Grotesmurf696/ZUIN/reports and protocols/Develop III/Rapport  CMF 02.pdf

# Protocol CMF usertests

# Project informatie

Projectnaam: Zuin
Zuin is een slim product voor kinderen dat hen bewust maakt van verbruik in huis en hen stimuleert om de interactie aan te gaan met hun ouders om energiezuiniger te leven.

Interviewer:
- Sam Verkimpe (Sam.Verkimpe@UGent.be), Student Industrieel Ingenieur Industrieel Ontwerpen
- Maxim Depever (Maxim.Depever@UGent.be), Student Industrieel Ingenieur Industrieel Ontwerpen
- Jitse Van Laer (Jitse.VanLaer@Ugent.be), Student Industrieel Ingenieur Industrieel Ontwerpen

# Algemeen

Het ZUÏN horloge bestaat uit een aantal kenmerkende onderdelen, zo heb je het bandje en de body die uit verschillende materialen gemaakt kan worden, de tactile ring die een verischillend patroon en tactile feel kan hebben als ook de finish van de body en het scherm.
Tijdens deze usertest gaat een groep kinderen opgedeeld worden in kleinere groepen. Ze krijgen de mogelijkheid om gedurende een bepaalde periode naar alle prototypes te kijken en ze uit te testen. Waarna ze een vragenblad kunnen invullen over de prototypes die ze net getest hebben. Erna volgt nog een kort vragenrondje om wat randinformatie te weten te komen over kleuren.

# Recrutering

Doordat Sam een aantal jaar leiding heeft gegeven in de scouts was er de mogelijkheid om via de huidige leiding een mail te laten rondsturen naar de ouders van de leden die in de “Woudloper” tak zitten. De leden binnen deze tak zijn hier max. 12 jaar oud, dus dit is de perfecte tak om testen uit te voeren. Aangezien de leden elke zondag activiteit hebben op de scouts zou het makkelijk zijn om met een selecte groep kinderen een half uurtje vroeger af te spreken om zo net voor de activiteit de usertest af te nemen.
Hieronder (zie Figure 1)staat een kopie van de mail die via één van de huidige leiding van de woudlopers naar alle ouders gestuurd is. In de bijlage van deze mail stond dan ook de informed consent die de ouders konden ondertekenen.

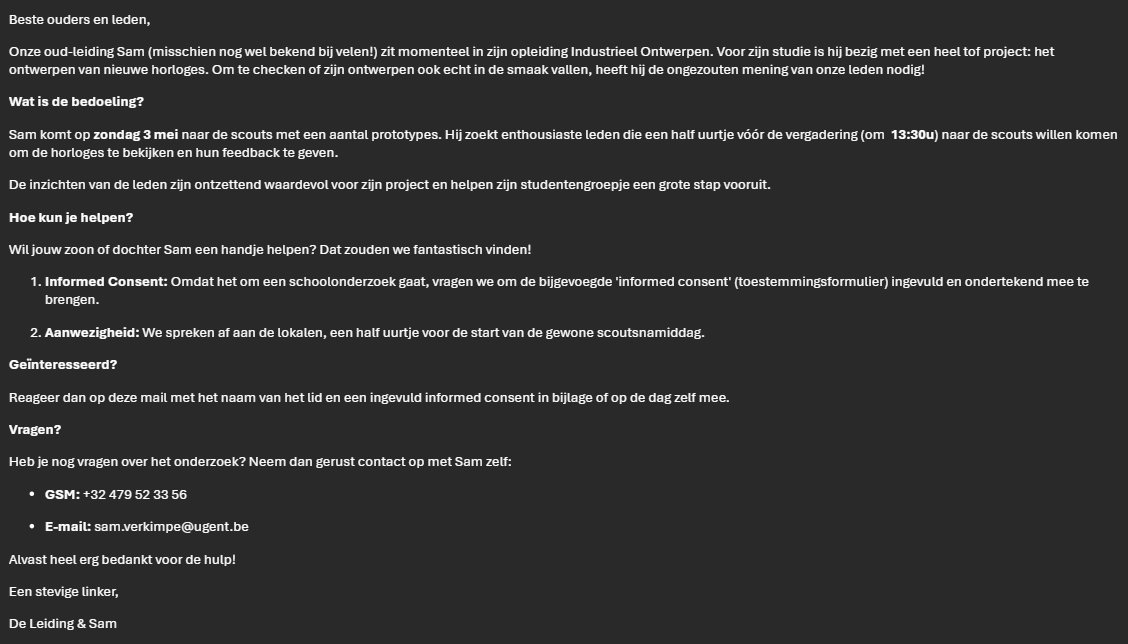
[picture p4: figure]

Figure 1: Rectuteringsmail
Door beperkte reactie op de mail was er besloten om de test met één week te verlaten naar zondag 10 mei, op 2 mei werd er na afloop van de activiteit een flyer uitgedeeld die de kinderen mee naar huis konden nemen. Zo wisten de kinderen van de activiteit en zouden zij zo rechtstreeks de ouders aan kunnen spreken voor op deze manier hopelijk toch een stuk meer respondenten te krijgen. Op onderstaande afbeelding (zie Figuur 1: Flyer voor leden) is de flyer te zien die de kinderen mee naar huis kregen.

# Respondenten (N = 3)

Kind | Leerjaar | Datum | Plaats
Enzo | 5 | 30/04/2026 | Scouts Wondelgem
Riven | 5 | 30/04/2026 | Scouts Wondelgem
Myron | 5 | 30/04/2026 | Scouts Wondelgem

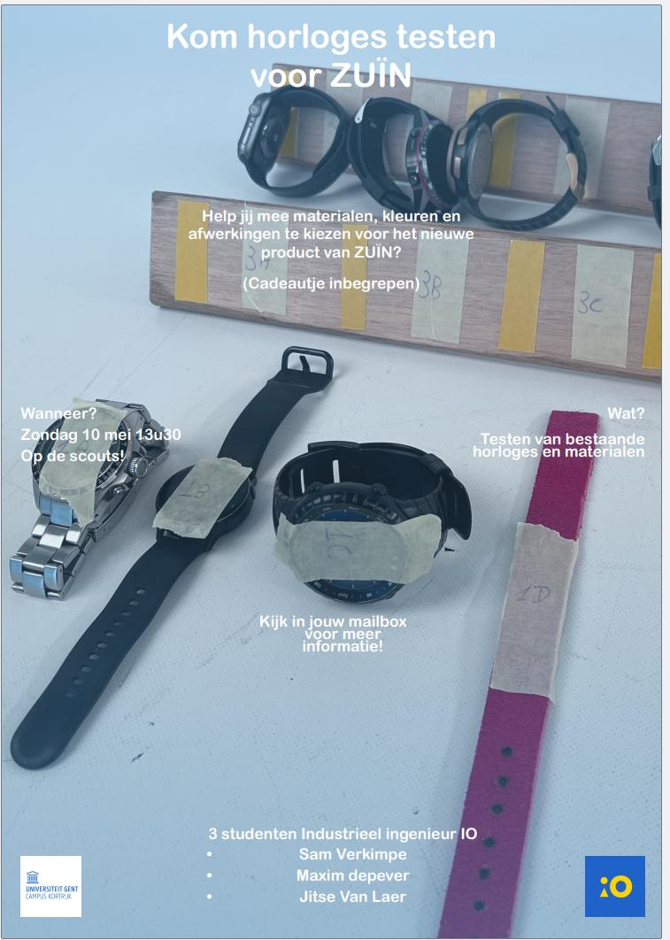
[picture p5: figure]

Figuur 1: Flyer voor leden

# Prototypes

Voor de testartefacten worden zowel zelfgemaakte prototypes als ook horloges van andere merken gebruikt. Dit zorgt ervoor dat er op een makkelijke manier een heel breed scala aan materialen en finishes getest kunnen worden. Voor het patroon op de ring worden er 4 body’s van horloge’s geprint. Elk van de 4 heeft een ander profiel op de ring, maar ook een andere taclite feedback. Voor het materiaal van de bandjes en de finishes van de body’s worden er horloges van andere merken gebruikt. De kinderen worden dan gevraagd om enkel naar één van de aspecten te kijken. Op onderstaande afbeelding (zie Figure 2) is de volledige testopstelling te zien van alle artefacten.

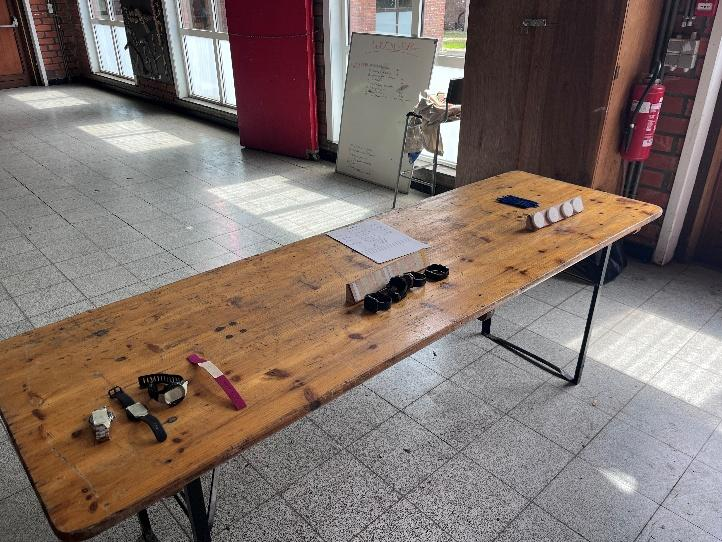
[picture p6: figure]

Figure 2: Testopstelling
Er zijn in totaal 3 “boards” met artefacten die de kinderen kunnen aandoen of waar ze aan kunnen voelen. Op deze manier is het makkelijker om de test op te delen in 3 groepen zodat elke groep telkens een ander deel van de gehele CMF ervaring test.

## Board 1

Bij deze setup is het de bedoeling dat de kinderen de artefacten (3 horloges en 1 prototype horloge bandje) rond hun pols doen en ze even goed voelen zodat ze god de verschillen tussen de bandjes merken. Op onderstaande afbeelding (zie Figure 3) zijn de 4 artefacten te zien, waaronder testartefact 1D. Dit bandje is gemaakt van een synthetisch leer. Het kleur van het bandje zelf speelt hier geen grote rol, maar vooral het gevoel rond de pols.

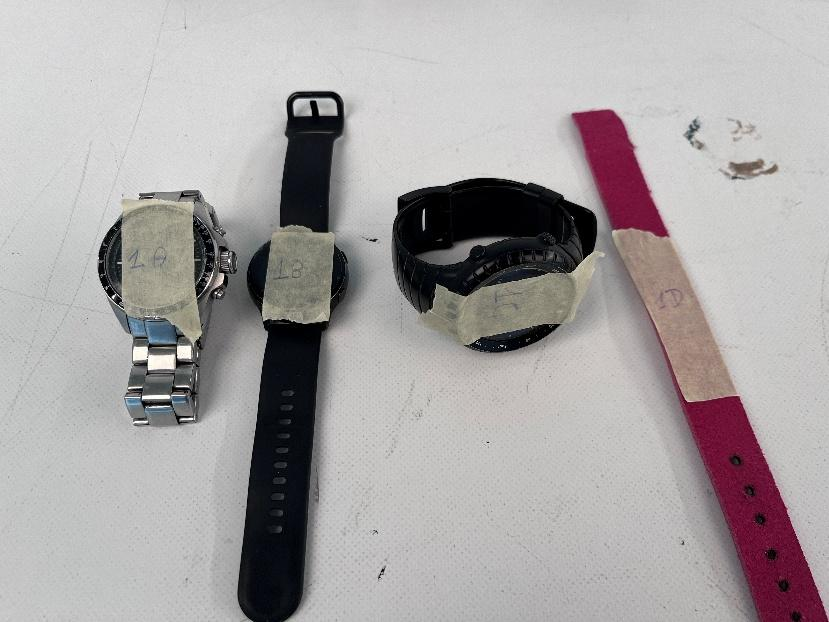
[picture p7: figure]

Figure 3: Board 1

## Board 2

Op Board 2 zijn 4 horloges te zien, dit zijn zowel smartwatches als normale digitale horloges. Hier moeten de kinderen kijken naar het materiaal en de finishes waarvan de body’s gemaakt zijn. Ook de afwerking op de knoppen speelt hier een rol. De kinderen mogen voelen aan de horloges, maar de horloges aandoen wordt hier niet gedaan. Op onderstaande afbeelding (zie Figure 4) is het 2de board te zien.

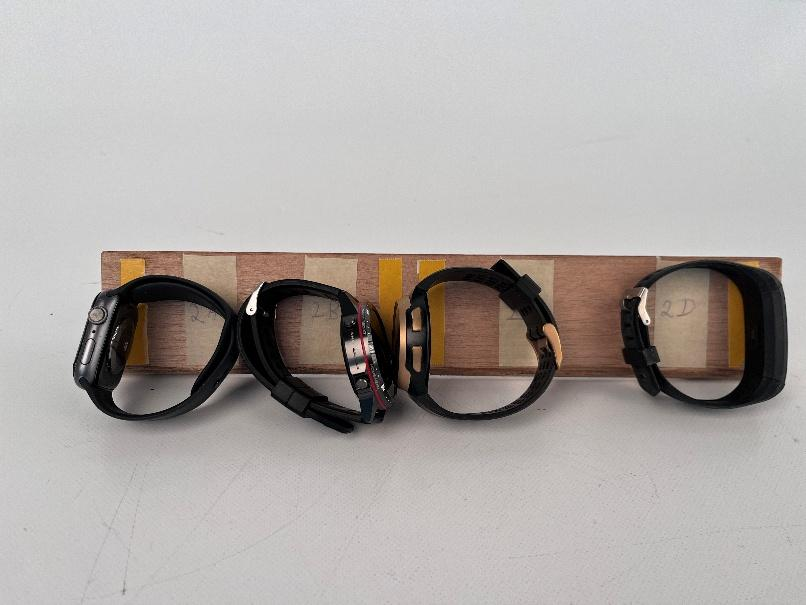
[picture p8: figure]

Figure 4: Board 3

## Board 3

Op board 3 worden de 4 verschillende prototypes van body’s geplaatst. De kinderen kunnen hier draaien aan de ringen van de body’s en op deze manier voelen hoe de afwerking op de ring is, als ook hoe de tactile feedback van de draaibeweging zelf is.

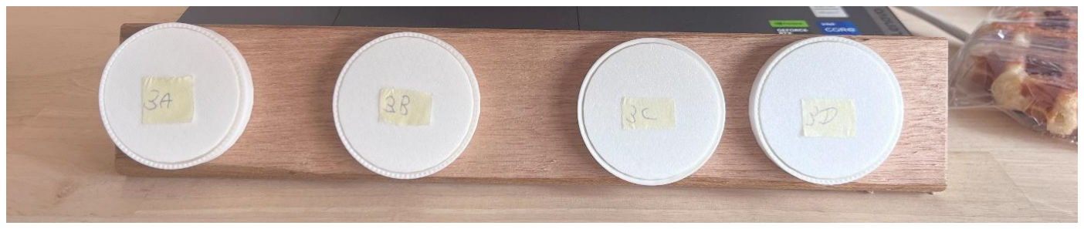
[picture p9: figure]

# Vragenlijst

Tijdens het testen worden de kinderen gevraagd om een vragenlijst in te vullen. Via deze vragenlijst willen we beter te weten komen wat de kinderen van de verschillende prototypes. Ze worden gevraagd om via een likertscale aan te duiden wat en hoe ze de verschillende prototypes ervaren. In bijalge zijn alle vragenlijsten te zien.

# Rapport

Het rapport van deze usertest is hier te vinden: CMF_Rapport_Develop2.pdf (https://ugentbe-my.sharepoint.com/:b:/g/personal/sam_verkimpe_ugent_be/IQCc59gRmQsRSLWiW1mBbghMAdhwbeE4el2uZ555LbgcBAo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)

# Vragenlijst

De vargenlijst voor de leden is hier te vinden: Vragenlijst voor leden.pdf (https://ugentbe-my.sharepoint.com/:b:/g/personal/sam_verkimpe_ugent_be/IQAT-k2qmfA6Qpb_IdjVv9tHARlVMj0OQpazggyW6qtySMU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)
