Grotesmurf696/ZUIN/img/Flyer voor leden_V2.pdf

# Kom horloges testen voor ZUÏN

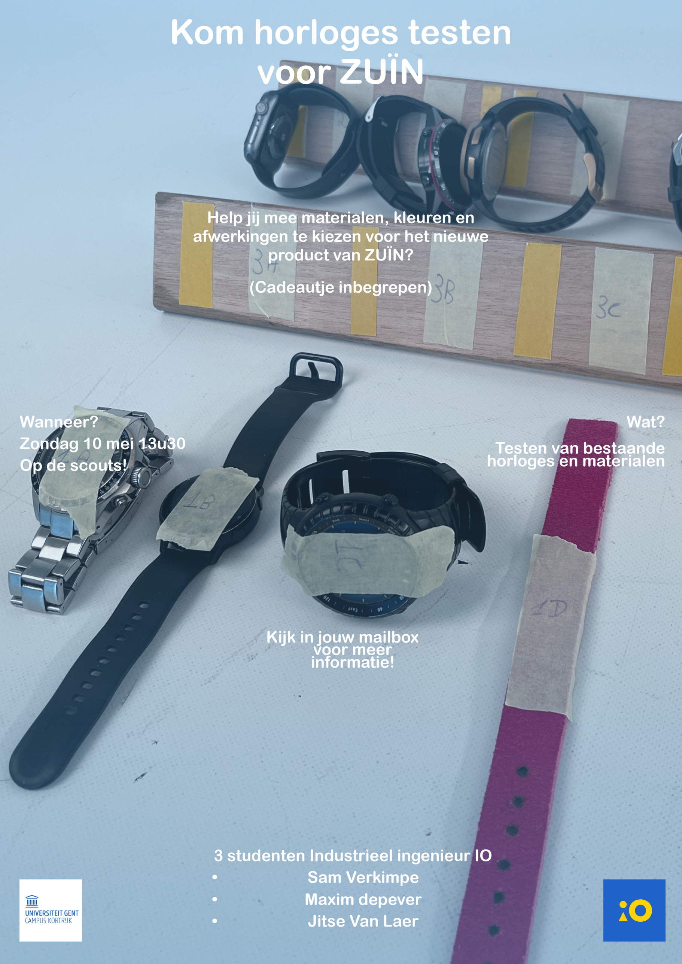
[picture p10: page 1]

Wanneer?
Zondag 10 mei 13u30
Op de scouts!

Wat?

Testen van bestaande
horloges en materialen

Help jij mee materialen, kleuren en afwerkingen te kiezen voor het nieuwe product van ZUÏN?

(Cadeautje inbegrepen)

### 3 studenten Industrieel ingenieur IO

- Sam Verkimpe
- Maxim depever
- Jitse Van Laer

Kijk in jouw mailbox
voor meer
informatie!
