Grotesmurf696/ZUIN/reports and protocols/Develop I/Rapport interview develop I.pdf

# Interview report – develop 1 (N=5)

## Project informatie

Projectnaam: Zuin
Zuin is een slim product voor kinderen dat hen bewust maakt van verbruik in huis en hen stimuleert om de interactie aan te gaan met hun ouders om energiezuiniger te leven.

Interviewer:
- Sam Verkimpe (Sam.Verkimpe@UGent.be), Student Industrieel Ingenieur Industrieel Ontwerpen
- Maxim Depever (Maxim.Depever@UGent.be), Student Industrieel Ingenieur Industrieel Ontwerpen
- Jitse Van Laer (Jitse.VanLaer@Ugent.be), Student Industrieel Ingenieur Industrieel Ontwerpen

## Doelstelling en kadering

In het 1ste deel van de develop-fase wordt ingezet om van concept naar een onderbouwde functionele architectuur te gaan. Er wordt dieper gezocht naar de koopbereidheid van het product. Verder wordt er ook ingegaan op de gewenste functionaliteiten waarvan enerzijds de ouders denken dat hun kind het leuk gaat vinden en anderzijds de functies die de ouders overtuigen om het product te kopen voor hun kind.

## Methode + reden

In het eerste deel van de Develop-fase is bewust gekozen om gebruikersinterviews af te nemen, maar deze keer gericht op de ouders. Dit zijn namelijk de personen die effectief de stap moeten zetten om het product te kopen. In de interviews werd de koopbaarheid afgetoetst. Verder werd er aan de hand van card sorting gekeken welke functies de ouders interessant vinden en een meerwaarde vinden aan het product. Uiteindelijk werd er nog gevraagd achter de ervaringen met habit changing products en de invloed hiervan. Er werd gekozen om interviews af te nemen om zo in gesprek te kunnen gaan met de ouder en door te vragen op bepaalde interessante antwoorden en keuzes.

## Protocol

Interview - protocol.docx (https://ugentbe-my.sharepoint.com/:w:/g/personal/sam_verkimpe_ugent_be/IQB2XM7peNSuRbQRF3uczHEGATVunaRYGWqFntXtGxvA77w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)

## Respondenten

- Steekproefomschrijving (N = 5)
De respondenten zijn ouders die kinderen hebben in de lagere school. Ze werden gecontacteerd via de lagere school van hun kind om vrijwillig deel te nemen aan dit interview.

## Interview

Interview 1: Sara

1. Huidige houding tegenover duurzaamheid & verbruik
- Niet actief aanwezig in gezingsleven
- Tijd en mentale ruimte ontbreken om hier actief mee bezig te zijn
- Wel de standaarddingen, zoals lichten uitdoen & verwarming regelen
- Facturen worden niet geanalyseerd
- Ze vindt het wel belangrijk voor de toekomst van haar kinderen, vooral gezien de stijgende energieprijzen
- Kinderen worden thuis toch weinig betrokken
- Op school wordt wel al een basis aangeleerd
2. Koopbaarheid
- Niet spontaan kopen -> ze is zelf niet actief of bewust bezig met energieverbruik & duurzaamheid
- In een bundel (bv via energieleverancier) is drempelverlagend
- Extra optie bij dienst maakt bewuster
- Extra info zou helpen
Ouder | Leeftijd Kind | Zonnepanelen? | Datum | Plaats
Sara | 12 & 8 | Nee | 28/2/2026 9u | Thuis
Marie | 8 | Ja | 28/2/2026 10u | Thuis
Lena | 5 & 8 | Ja | 28/2/2026 11u | Thuis
Bram | 5 & 6 | Nee | 2/3/2026 10u | Online
Jonas | 4 & 7 | Ja | 5/3/2026 20u | Online

3. Functies
- Minder aantrekkelijk
- Sterke prikkels
- Fysieke knoppen ->
touchscreen voelt actueler
- Aantrekkelijk
- Virtueel huisdier -> speels & motiverend
- Challenges
- Gezinscompetitie
- Subtiel geluidje bij over verbruik

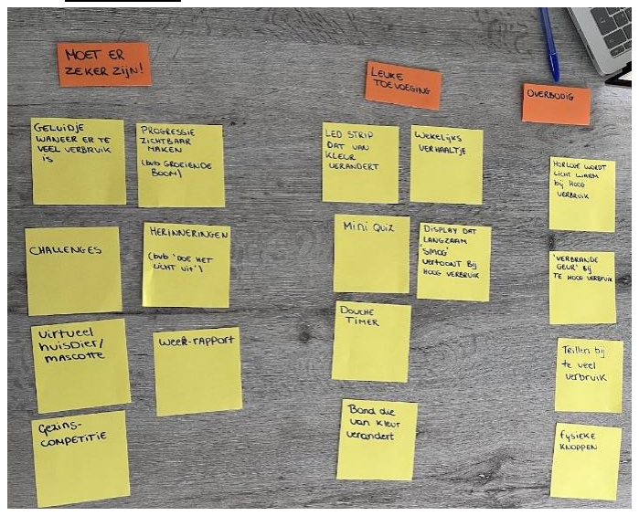
[picture p59: figure]

4. Ervaringen met smart devices & habit changing products
- Probeerde recent kleine “geluksmomenten” op te schrijven, maar hield dat slechts enkele dagen vol
- Ze is een overdenker
- Tijdsgebrek

Interview 2: Marie

1. Huidige houding tegenover duurzaamheid & verbruik
- “Waarschijnlijk te weinig”
- Wel de basisdingen
- Lichten uitdoen
- Verwarming instellen
- Huis geïsoleerd
- Zonnepanelen
- Partner houdt zich wel actief bezig met facturen en verbruik
- Ze kiest bewust voor praktisch gemak & rust in haar hoofd -> bijvoorbeeld niet altijd rekening kunnen houden met zonne-uren
- Dochter leert op school over duurzaamheid
- Ze zou haar houders aanspreken op lichten laten branden
2. Koopbereidheid
- Afhankelijk van de prijs
- Eerder zelf kopen dan via een energieleverancier
- Kan er dan makkelijker meer info over zoeken
- “Dan denk ik: Amai, wat willen ze ons weer smeren?”
- Via leverancier voelt gepusht

3. Functies
- Minder aantrekkelijk
- Trillen (enkel als het verbruik echt extreem is -> afhankelijk
van hoe vaak)
- Te veel visuele prikkels
- Overmatige ‘nieuwe’ functies
- Complexe of flashy features
- “Ik ben zo wel doe-maar-gewoon-normaal”
- Aantrekkelijk
- Virtueel huisdier
- Zichtbare progressie
- Belonen

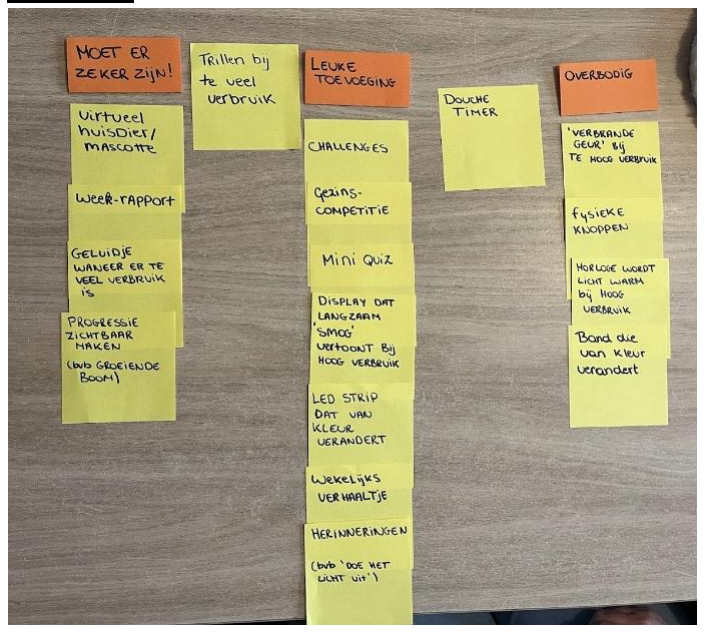
[picture p60: figure]

4. Ervaringen met smart devices & habit changing products
- De kinderen hadden vroeger speelgoed zoals een virtueel diertje (Bitsy)
- Intens gebruik in begint -> daarna in speelgoedbak
- “Ik denk dat dat met zo'n horloge ook zou kunnen, dat dat na een maand of zo gedaan is geweest. Maar als je dat aandoet, dan kun je dat al niet kwijt geraken.”
- Geen slimme energiemeters, app van zonnepanelen wordt niet opgevolgd, geen actieve monitoring van verbruik
- Dochter heeft een slaapdagboek
- Houdt dit enkel vol als de mama het begeleidt

Interview 3: Lena

1. Huidige houding tegenover duurzaamheid & verbruik
- Maakt zelf wasmiddel
- Probeert vaker de fiets te nemen
- Zonnepanelen
- Probeert wasmachine & vaatwasser te plannen op zonnige momenten
- Spreekt haar kinderen actief aan op lichten uitdoen
- Kinderen doen goed meer
2. Koopbereidheid
- Ze zou het misschien kopen als de kinderen ouder zijn
- Als app zou het meer aanspreken
- Kinderen gaan ook spelletjes willen spelen op het horloge niet enkel de tijd zien

3. Functies

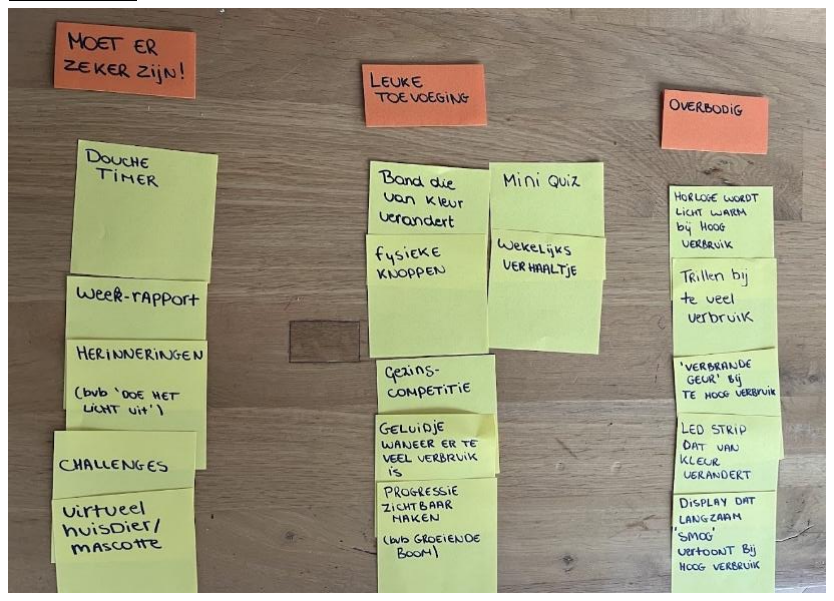
[picture p61: figure]

- Minder aantrekkelijk
- Trillen bij hoog verbruik -> went mogelijk snel
- “Ik denk dat dat na een tijd ook niet meer opvalt als dat afgaat.”
- Afleiding mag niet overheersen
- Aantrekkelijk
- Virtueel huisdier
- Challenges
- Douche timer -> herkenbaar probleem
- Rapport / overzicht
- Herinneringen
4. Ervaringen met smart devices & habit changing products
- Zoon heeft een bitsy = tamagotchi-achtig diertje waarvoor je moet zorgen
- Virtuele diertjes zijn gekend en positief ervaren (zoomorphisme)
- Zelf enkel een app voor zonnepanelen en elektriciteit app
- Geen actieve monitoring
- Nog nooit een dagboek of langdurige tracking geprobeerd
- “Ik ben misschien te chaotisch daarvoor”
- “Als ik met iets nieuws begin, houd ik het niet lang vol”

Interview 4: Bram

1. Huidige houding tegenover duurzaamheid & verbruik
- Focust op verspilling te beperken & kinderen worden erop aangesproken
- Lichten uitdoen
- Kraan dichtdraaien
- Geen eten/drinken laten staan => bewust aankopen doen
- Niet dagelijks vlees eten

- Duurzaamheid zit in gewoontes, niet in grote spectaculaire acties
2. Koopbereidheid
- Leeftijd is een cruciale factor
- 5-6 jaar is te jong voor hem omdat kinderen op die leeftijd pas klok leren lezen
- Eerder geschikt voor wanneer kinderen het concept van geld begrijpen, wanneer ze oorzaak-gevolg kunnen koppelen en wanneer competitie hen echt motiveert
- Doelgroep rond 8-12 jaar
- “Ik vind dat een kind op zoveel mogelijk fronten moet proberen een
- kind te blijven, zonder te veel input of dingen waar ze eigenlijk in principe nog niet zoveel aan kunnen doen.”
- Product moet een competitief element bevatten en er moet een concreet doel aan gekoppeld zijn
3. Functies

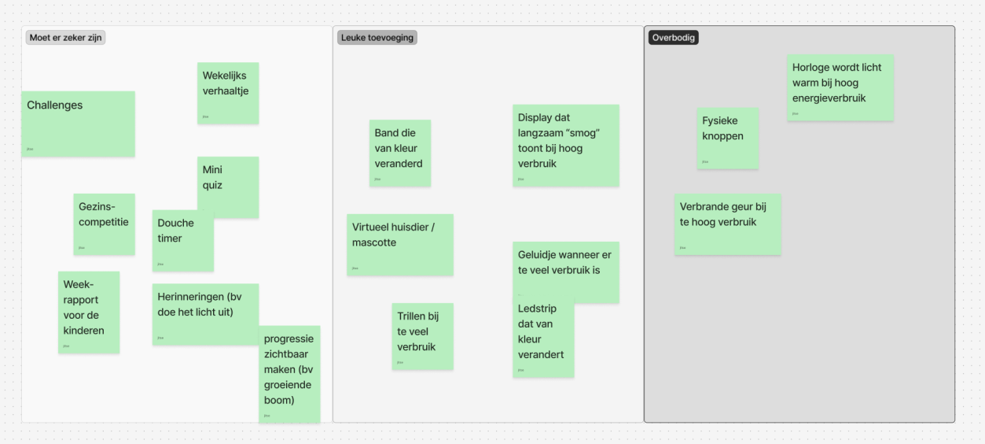
[picture p62: figure]

- Minder aantrekkelijk
- Trillen
- Constant signalen
- Warm worden
- Overmatige fysieke prikkels
- Aantrekkelijk
- Rapport
- Zichtbare progressie
- Quiz of verhaaltje met educatieve waarde
- Meetbaar resultaat
- Competitie
- Concreet doel
- “Wat ik het belangrijkste vind is dat er wel effectief een resultaat wordt gekoppeld aan het doel, maar het resultaat moet ook iets bijleren, natuurlijk.”

4. Ervaringen met smart devices & habit changing products
- Willen in de toekomst verwarming, zonnepanelen en hun energiebeheer in 1 systeem koppelen (hebben net een nieuw huis)
- Habit changing products: trainingsschema & budgetbeheer
- Tools werken alleen als ze zichtbaar aanwezig zijn
- “Als ik iets moet opendoen om dat dan te doen, dat gaat niet. Als ik dat zie of dat is bijvoorbeeld een smartbord of iets van dienen aard, dan gaat dat vanzelf.”

Interview 5: Jonas

1. Huidige houding tegenover duurzaamheid & verbruik
- Bezig maar op gezond verstand
- Zonnepanelen -> wasprogramma’s daarop afstemmen
- Elektrische auto’s
- Geen onbewust stroomverbruik
- Hoort bij orde & netheid in opvoeding
- In onderbewustzijn
- Elektriciteit nog moeilijk want is iets onuitputtelijk voor hen
- Toestellen op batterijen zijn wel meer begrijpbaar
2. Koopbereidheid
- De gamification (de badges & notifications) werkt bij kinderen
- Als ouder niet direct kopen want kinderen moeten het concept van energie nog leren, om handelingen te koppelen aan verbruik (bv dat koken een piekmoment zal zijn) moeten ze ouder voor zijn
- Alles van wearables als ouder wel nadenken wat er met gegevens wordt gedaan -> als je dit gratis krijgt bij energieleverancier gaan zij misschien deze datapunten kunnen gebruiken -> extra over nadenken
3. Functies

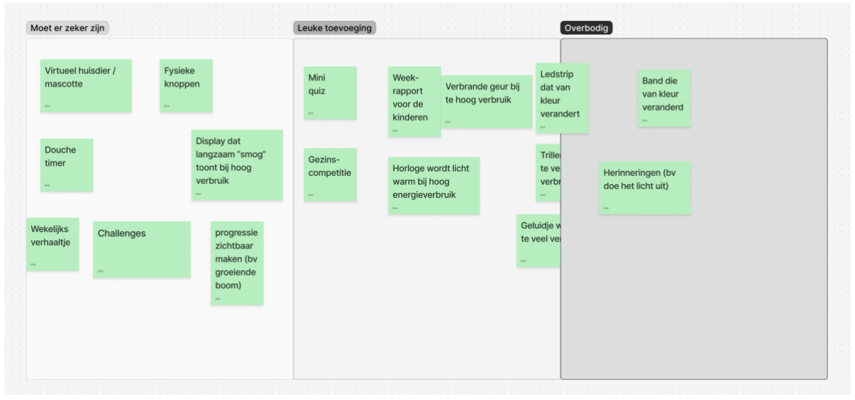
[picture p63: figure]

- Minder aantrekkelijk
- “Mensen krijgen al zoveel notificaties en prikkels, die constante dopamine toevoer daar is de grens klein tussen leuke toevoeging of storend”
- Aantrekkelijk
- Mini quiz -> als je zo engagement kan controleren is dat wel leuk
- “Algemene doelstelling moet tof zijn, niet verslavend, reclame of datapunten zijn -> in die optiek denk ik dat challenges wel nen toffe is, maar dan moet het wel op individueel vlak in huis zijn niet connected met klasgenootjes. Bij volwassenen werk dit ook (smartwatch)”
- Verhaaltje is feature dat het hardste resoneert omdat je op een slimme manier kennis bijbrengt
4. Ervaringen met smart devices & habit changing products
- Kinderen hebben nog geen smart devices voor hunzelf
- Zelf ook geen smart devices om verbruik te meten -> denken zelf genoeg te weten
- Doet mee aan challenges van smartwatch maar puur voor zichzelf

## Informed consent

informed consent.docx (https://ugentbe-my.sharepoint.com/:w:/g/personal/sam_verkimpe_ugent_be/IQCaxyvEQGZjS44UdRJrZvIUATTRFuRnWEUWwswbVG1b3xE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)

## Conclusie

Op basis van de vijf interviews met ouders van kinderen in de lagere school komen enkele duidelijke inzichten naar voren die richting geven aan de productvereisten van Zuin.

### 1. Doelgroep en positionering

De meest geschikte doelgroep voor het product ligt volgens de respondenten bij kinderen tussen 8 en 12 jaar. Op jongere leeftijd moeten kinderen het begrip ‘verbruik’ nog leren. Pas wanneer kinderen oorzaak-gevolgrelaties beter begrijpen en gemotiveerd worden door competitie of doelen, kan het product effectief gedragsverandering stimuleren.

Daarnaast blijkt dat ouders duurzaamheid wel belangrijk vinden, maar dat het niet altijd actief aanwezig is in het dagelijks gezinsleven. Tijdgebrek, mentale belasting en andere prioriteiten zorgen ervoor dat energieverbruik vaak slechts oppervlakkig wordt opgevolgd en dat enkel de logische dingen worden uitgevoerd zoals het licht uitdoen. Het product moet daarom laagdrempelig en intuïtief zijn, zodat het geen extra belasting vormt voor ouders.

### 2. Koopbereidheid en distributie

De koopbereidheid van ouders is sterk afhankelijk van:
- Prijs
- Toegevoegde waarde voor het kind
- Gebruiksgemak
- Transparantie rond data en privacy

De meningen om het product via een energieleverancier of ander abonnement te verkrijgen zijn verschillend: sommige ouders zouden het product eerder zelfstandig kopen om zelf informatie te kunnen opzoeken, terwijl anderen aangeven dat een bundel via een energieleverancier de instapdrempel kan verlagen. Belangrijk is dat het product niet aanvoelt als een marketinginstrument van energieleveranciers.

### 3. Belangrijkste gewenste functionaliteiten

Uit de card sorting en gesprekken komen enkele functies duidelijk naar voren als waardevol:

Sterk gewaardeerde functies
- Virtueel huisdier (speelse motivatie)
- Challenges
- Gezinscompetitie
- Zichtbare progressie of resultaten
- Beloningen of badges
- Rapporten/overzichten van gedrag
- Educatieve elementen zoals quizzen of verhaaltjes
- Praktische functies zoals een douche-timer

➔ Deze functies combineren gamification, educatie en zichtbare impact, wat volgens ouders het meest motiverend is voor kinderen.

Minder gewenste functies

Ouders geven aan dat het product niet te veel prikkels mag bevatten. Negatieve reacties kwamen vooral op:

- Constant trillen of notificaties
- Overmatige visuele of auditieve prikkels
- Te complexe of flashy features
- Te veel fysieke signalen

➔ Het product moet dus subtiel, rustig en niet storend blijven, zodat het op lange termijn bruikbaar blijft.

### 5. Langdurig gebruik en gedragsverandering

Een belangrijk inzicht is dat veel habit-changing producten slechts kort intensief gebruikt worden. Na de eerste interesse verdwijnt het gebruik vaak snel. Om langdurige betrokkenheid te stimuleren moet het product:

- duidelijke doelen bieden
- progressie zichtbaar maken
- een speels element behouden
- regelmatig nieuwe uitdagingen aanbieden
- tegelijk niet verslavend of overweldigend zijn
- Ook blijkt dat begeleiding van ouders een rol speelt in het volhouden van nieuwe gewoontes.

### 6. Ontwerpimplicaties

De inzichten uit de interviews leiden tot enkele belangrijke ontwerpprincipes:

- Simpel en intuïtief ontwerp
- Speelse gamification (bv. virtueel huisdier)
- Educatieve content geïntegreerd in het spel
- Meetbare en zichtbare impact
- Beperkte en subtiele notificaties
- Focus op gezinscontext i.p.v. externe competitie
- Respect voor privacy en data
