Grotesmurf696/ZUIN/reports and protocols/Develop III/Protocol UX - develop III.pdf

# UX & Service Design – Develop 3

Project informatie
Projectnaam: Zuin
Zuin is een slim product voor kinderen dat hen bewust maakt van verbruik in huis en hen stimuleert om de interactie aan te gaan met hun ouders om energiezuiniger te leven.

Onderzoekers:
- Sam Verkimpe (Sam.Verkimpe@UGent.be), Student Industrieel Ingenieur Industrieel Ontwerpen
- Maxim Depever (Maxim.Depever@UGent.be), Student Industrieel Ingenieur Industrieel Ontwerpen
- Jitse Van Laer (Jitse.VanLaer@Ugent.be), Student Industrieel Ingenieur Industrieel Ontwerpen

## Emotioneel ontwerp

“Welke emoties moet het product oproepen?”

- Ouders
o Trots -> kind leert zelf over verbruik en denkt er zelf over na
o Opluchting -> minder discussie (“doe het licht uit!”, “korter douchen!”) o Samenwerking -> niet meer ouders vs kinderen maar samenwerken
- Kinderen
o Autonomie -> kind kan zelf beslissen om minder te verbruiken
o Uitdaging -> beter doen dan gisteren
o Verbondenheid -> in gesprek gaan met de ouders
-> verbonden met horloge/ virtuele vriend o Trots -> ze doen iets goed (zonder dat de ouders erachter zitten) o Begrip -> ze leren meer over verbruik

Mogelijke valkuilen:
o Schuldgevoel -> “Ik verbruik te veel”

Mascotte

Methode + reden
De verbondenheid tussen het kind en het horloge kan bevorderd worden door gebruik te maken van antropomorfisme.
“Anthropomorphism = attributing human qualities to non-human beings, inanimate objects”
Er wordt dus gewerkt met een mascotte die het kind doorheen het horloge begeleidt, tips geeft en aanmoedigt. Dit wordt dus een vriendje voor het kind.

Omdat het belangrijk is dat het kind deze mascotte als een vriend ziet, en er dus waarde aan hecht en zich er verbonden mee voelt, wordt er eerst een deskresearch gedaan naar de belangrijke aspecten van zo een virtuele vriend.

Vervolgens wordt een er interview afgenomen met kinderen om zo in de leefwereld van de doelgroep te geraken en ook met hen te testen waar zij zich verbonden bij voelen.

Deskresearch
Prompts
o Antropometrische trends bij kinderen o Zoomorphisme trends kids
o Friendly monsters theory
o Mascot children theory
o Trends games 8-12y
Interview
- Steekproefomschrijving (N = 5 )
De respondenten zijn kinderen van het 4e

, 5e

en 6e
leerjaar die vrijwillig wilden deelnemen. Eerst zijn de leerkrachten van de klassen gecontacteerd met de vraag of zij met hun klas wilden deelnemen. Vervolgens verzonden zij een mail naar de ouders en kinderen van hun klas om vrijwilligers te zoeken die tijdens de les of middag kort geïntervieuwd wilden worden.
Kind | Leerjaar | Datum | Plaats
Mila | 4 | 30/04/2026 | Basisschool Klim-Op Grobbendonk
Jana | 4 | 30/04/2026 | Basisschool Klim-Op Grobbendonk
Sterre | 4 | 30/04/2026 | Basisschool Klim-Op Grobbendonk
Jarne | 4 | 30/04/2026 | Basisschool Klim-Op Grobbendonk
Simon | 4 | 30/04/2026 | Basisschool Klim-Op Grobbendonk

- Voorbeeld personages
Deze werden gecreëerd door enkele prompts in ChatGPT te in te geven
o Teken voor mij 5 monstertjes, elk in een andere kleur, met een ander kenmerk bv een bril, om als zoomorphistische mascotte hen te begeleiden in een spel -> kinderen moeten zich hiermee verbonden voelen

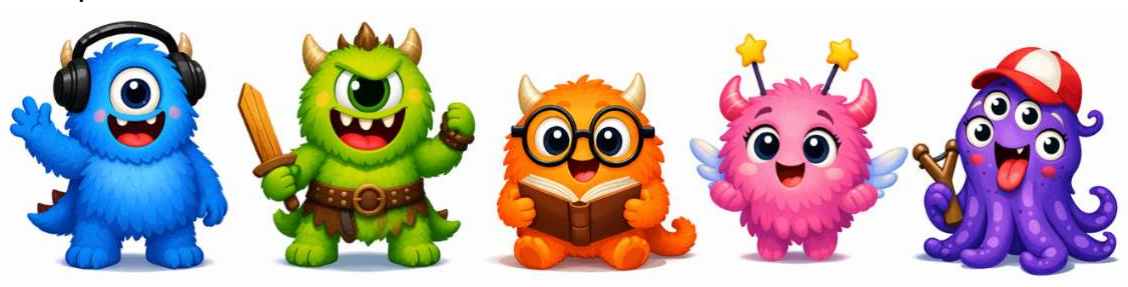
[picture p64: figure]

o ontwerp 5 personages geïnspireerd op kinderboeken/speelgoed voor kinderen van 8-12 jaar (geen mensen!!)

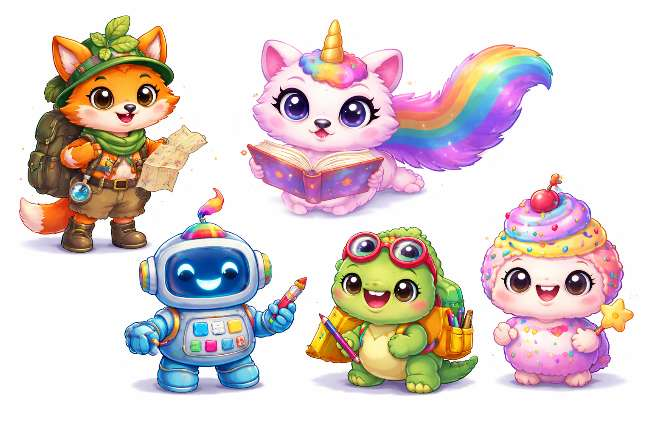
[picture p65: figure]

o ontwerp 10 NIEUWE karakters, geinspireerd op gumball / disney / ketnet / phineas and furb / animal crossing

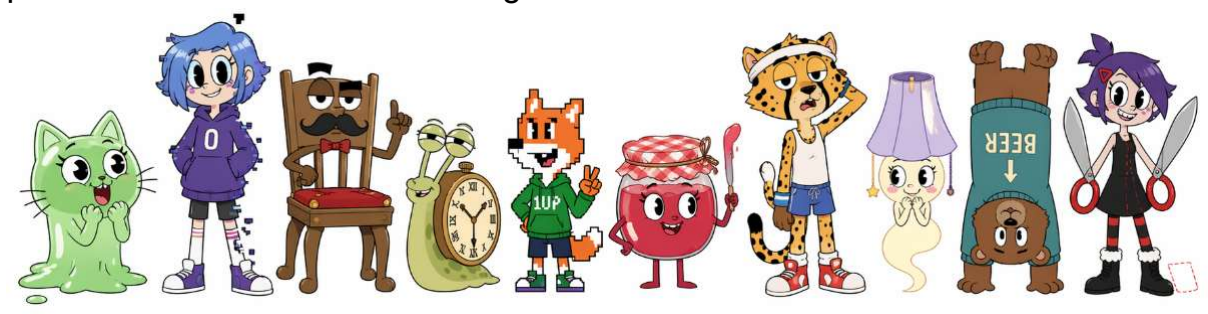
[picture p66: figure]
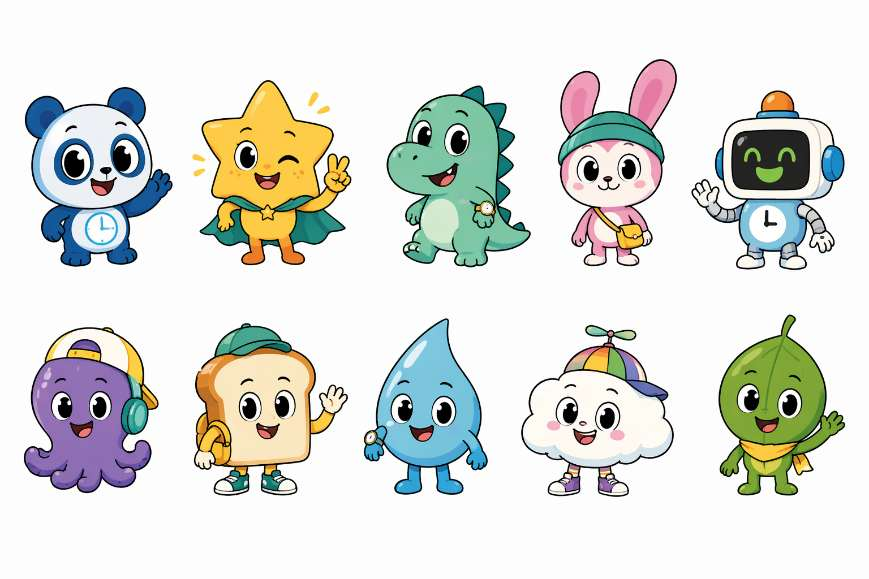
[picture p67: figure]

o maak nog 10 zo'n karakters geschikt als mascotte op een kinderhorloge o nog 1x, geïnspireerd op al het vorige, maak 5 mascottes in die stijl met als doel op een kinderhologe (8-12jaar) dat bezig is met duurzaamheid

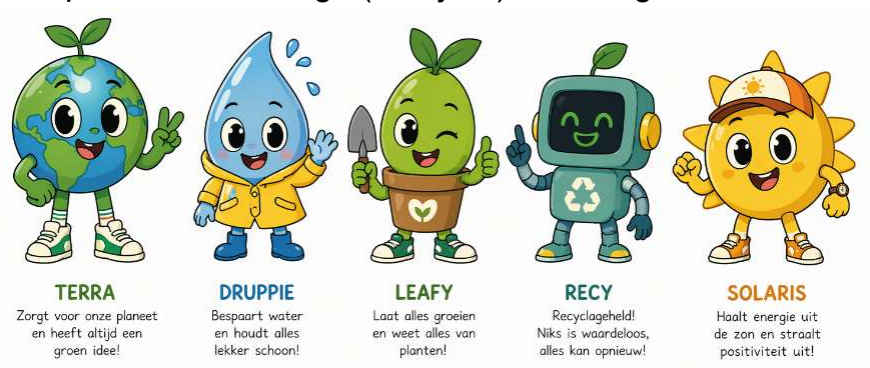
[picture p68: figure]

- Interview (+/- 40 min)
Deel 1 (5’)
De kinderen krijgen allemaal een vriendboekformulier. Deze vullen ze in over hun favoriete personage uit de lijst.

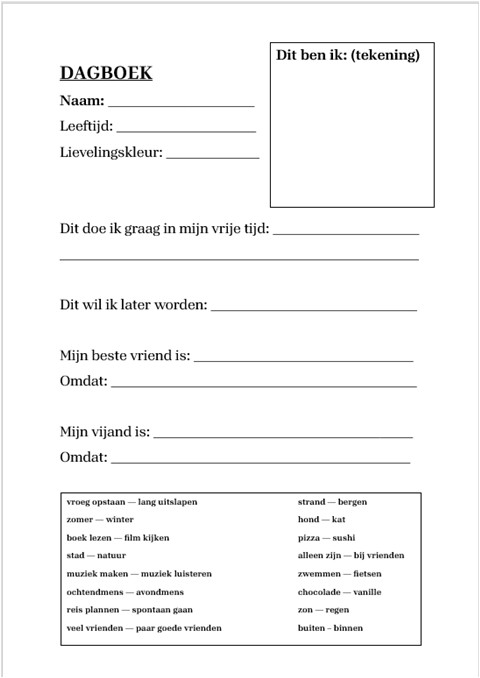
[picture p69: figure]

Vragen:
o De antwoorden die jullie hebben ingevuld, passen die ook bij jou?

Deel 2
De kinderen bespreken in groep de personages. Ze mogen deze groeperen: vriend, vijand, kennis, andere. Daarbij geven ze elk personage een naam.
Vervolgens lees ik enkele quotes voor, en schrijven ze voor zichzelf op wie dit gezegd zou kunnen hebben.

Quotes:
1) "Heeft iemand mijn sleutels gezien?"
2) "Wat een mooie dag."
3) "Dit is mijn plek. Zoek je eigen."
4) "Ik verveel me."
5) "Dat is het stomste idee dat ik ooit heb gehoord. Laten we het doen."
6) "Ik ben niet boos. Ik ben teleurgesteld. Wat erger is."
7) "Ik snap er niks van”
8) “Gaan we samen spelen?”
9) “Ik heb een geheim, maar je mag dit aan niemand vertellen.”
10) “Goed bezig!”

“Naar wie zou jij luisteren als hij/zij je een opdracht geeft?”

Interface eilanden

Methode + reden
Het horloge geeft het verbruik per kamer weer. Om deze kamers op een speelse, luchtige manier voor te stellen, kozen wij ervoor om elke kamer een eigen thema eiland te geven. Om te ontdekken waar kinderen nu fan van zijn, werd er gevraagd aan een klas van het 4e leerjaar en een klas van het 5e
leerjaar om allemaal hun droomeiland te ontwerpen. Hieruit zullen de veelvoorkomende elementen gehaald worden om zo een gemeenschappelijk droomeiland te bekomen. Vervolgens wordt dit met Vizcom tot leven gebracht.

Template

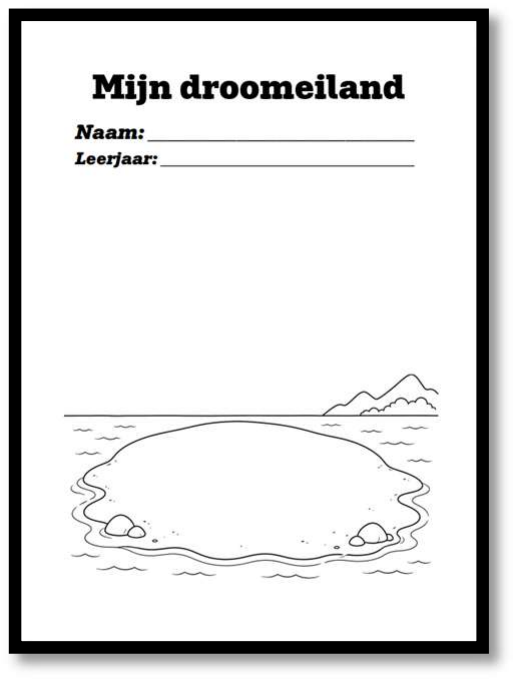
[picture p70: figure]

Interface + micro-interacties

Methode + reden
De interface moet gericht worden naar kinderen. Deze moet blijven verassen. Belangrijk is ook dat deze geen schuldgevoel brengt, maar hen motiveert. Dit wordt vooral gerealiseerd door micro-interacties. Hiervoor wordt gekeken naar sites, apps en tv-programma’s gemaakt voor kinderen van 8-12 jaar. Verder wordt er ook een deskresearch uitgevoerd om meer info te verkrijgen over de belangrijke aspecten aan een interface voor kinderen.

Sites, apps & tv-programma’s
o Ketnet
o Subway Surfer, Cut the rope, Animal crossing, Roblox
o Disney
o https://ixdf.org/literature/article/ui-animation-how-to-apply-disney-s-12-principles-of-animation-to-ui-design

Deskresearch prompts
- interface kids 8-12y
- apps design kids 8-12y

## Service design

Customer Journey
“Wat zijn de interacties vóór, tijdens en na het gebruik van het fysieke object?”
De customer Journey die eerder al gemaakt werd, wordt aangevuld met duidelijkere grenzen wat voor, tijdens en na het gebruik gebeurt. Ook worden er nog extra stappen toegevoegd die eerder misschien over het hoofd gezien werden.

Service Blueprints
“Hoe zijn verschillende actoren betrokken bij de ‘value delivery’”
Er wordt een service blueprint-template aangemaakt. Het storyboard wordt uitgezet per frame. Hierbij wordt gekeken naar de fysieke acties die ondernomen worden en de achterliggende systemen die hierbij te pas komen.
