Grotesmurf696/ZUIN/reports and protocols/Discovery/Rapport competitor analysis_Sam.pdf

Rapport competitor analysis

# Project informatie

Onderzoeker: Sam Verkimpe, student Industrieel ontwerpen 3de bachelor.
Goal: Hoe kunnen slimme producten jonge gezinnen helpen de juiste duurzame keuzes te maken in verband met elektrische energie zonder grote cognitieve of financiële belasting. Onderwerp: Sustainability @ Home

# Onderzoeksdoel

Informatie verzamelen over bestaande oplossingen en hoe zij het probleem aanpakken en verwerken tot een product. Welke verschillen zijn er tegenover de verschillende producten en hoe voldoen zij aan de vooropgestelde criteria (zie ). Er kan geleerd worden uit hun oplossingen om deze toe te passen op mijn uiteindelijke eerste ontwerp.

# Motivatie onderzoeksmethode

Om wat meer te weten te komen over de bestaande oplossingen voor een bepaald probleem is het slim om een competitor analysis te doen. Er kan makkelijk gezien worden hoe zij inspelen op de markt en de doelgroep. Ook kunnen bepaalde designkeuzes ons ook wat meer zeggen over op welke problemen deze bedrijven gebotst zijn tijdens de ontwikkeling van hun product. Ook is het natuurlijk dat mijn product uiteindelijk uitspringt boven deze van de competitie en dan is competitor analysis dé manier om te weten te komen hoe dit kan.

# Protocol

Link: Protocol competitor analysis.docx (https://ugentbe-my.sharepoint.com/:w:/g/personal/sam_verkimpe_ugent_be/EeYlcvRcFO5FtuqpWi-H_BYBnhVSppKV_AyAEDK1M_NLag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)

# Resultaten

## Producten:

Product | Bedrijf | Link
GEO Trio II Energieverbruiksm onitor | Eco-Logisch | https://www.eco-logisch.nl/kennisbank/Geo
HomeWizard P1 Meter | HomeWizard | Homewizard.com
TP-Link Tapo P115 Slimme Stekker | TP-Link | https://www.tink.nl/p/tp-link-tapo-p115-4-pack
Slimme stopcontacten met kinderbeveiliging | Pallo.be | https://pallo.be/slimme-stopcontacten-met-kinderbeveiliging-en-energiemeters (https://pallo.be/slimme-stopcontacten-met-kinderbeveiliging-en-energiemeters)
SlimmeMeterPortal .nl | SlimmeMeterP ortal | https://id.nl/zekerheid-en-gemak/verzekeringen-en-geld/energiecontract/meten-is-weten-zo-beperk-je-je-energieverbruik (https://id.nl/zekerheid-en-gemak/verzekeringen-en-geld/energiecontract/meten-is-weten-zo-beperk-je-je-energieverbruik)
Loxone Energiemonitoring | Loxone | https://www.loxone.com/nlnl/producten/energie/ener giemonitoring (https://www.loxone.com/nlnl/producten/energie/energiemonitoring)
Phoenix Contact EMpro modules | Phoenix Contact | https://www.phoenixcontact.com/nl-nl/producten/energiemonitoring (https://www.phoenixcontact.com/nl-nl/producten/energiemonitoring)

Tot nu toe 7 producten onderzocht.

## Overzicht Miro

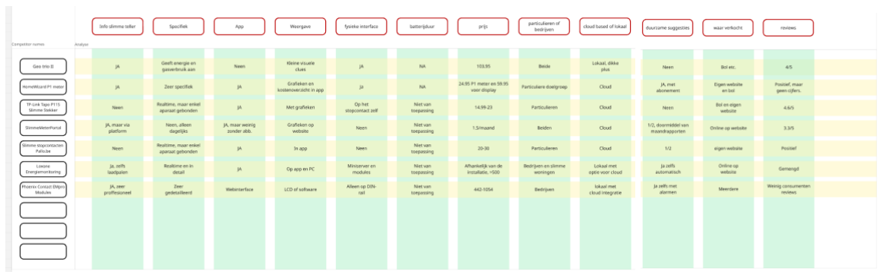
[picture p73: figure]

## Opvallende kenmerken per product

- Geo Trio II:

Afkomstig uit Engeland, maar zie vooral veel gebruik in Nederland. Het product geeft exact aan hoeveel stroom en gas je verbruikt en levert een kleine visualisatie (zie Figuur 1: Display Geo Trio II). Geeft ook aan hoe warm het is.
Belangrijk is dat deze meter volledig zelfstandig is en ook niet verbind met wifi, maar wel de mogelijkheid heeft tot verbinding om bijvoorbeeld software updates uit te voeren. Ook geven ze zelf aan dat “Door beter inzicht maak je slimmer gebruik van je energie en hierdoor bespaar je gemiddeld 6,9% op gas en 2,2% op elektriciteit! Op de lange termijn kan dit oplopen tot tientallen euro's per jaar.”. Maar ik zie hier zelf geen bewijs van.
- HomeWizard P1 meter:
Interessant is dat deze meerdere producten hebben. Of alleen de aansluiting op de meterkast, maar ook een fysiek scherm. Met een extra abonnement geeft deze jou ook extra instructies om duurzamer te zijn. Wat wel opvalt is dat dit bedrijf exact dezelfde gegevens weergeeft in verband met besparingen als de Geo Trio II, maar zei hebben wel een bronvermelding. Maar aangezien ze beiden exact dezelfde gegevens hiervoor gebruiken ben ik sceptisch.

# Conclusie

Veel van deze bedrijven hebben een zeer verfijnd product op de markt kunnen zetten. Maar geen enkel product scoort echt goed op elk vlak. Iets wat ik wel wil met mijn toekomstig product. Er zijn een aantal producten die beweren X% te besparen, maar die data lijkt van één of ander overheidsdocument geplukt te zijn (kan hier ook fout in zijn).
Concreet is naar mijn mening de markt van deze producten nog zeker niet overgesatureerd en is er nog veel mogelijkheid om te groeien. Ondanks dat er een aantal producten zijn die voor mij hoog scoren, is er geen enkel product die naast wat analytische data ook echt gepersonaliseerde verbruikerstips geeft en dat is echt wat ik wil bereiken. Ook heb ik wat leuke dingen gezien rond het al dan niet gebruik van Cloud mogelijkheden.

# Bijlagen

- Geo Trio II dysplay

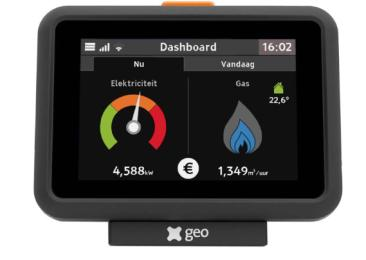
[picture p74: figure]

Figuur 1: Display Geo Trio II
