Grotesmurf696/ZUIN/reports and protocols/Discovery/Rapport literatuur review_Sam.pdf

# Rapport literatuur review

# Project informatie

Onderzoeker: Sam Verkimpe, student industrieel ontwerpen 3de bachelor
Goal: Hoe kunnen jonge gezinnen geholpen worden om meer inzicht te krijgen in hun energieverbruik, om zo bewuster te verbruiken?
Onderwerp: Sustainability @ Home

# Onderzoeksdoel

Informatie zien te vergaren over het energieverbruik bij jonge net alleenwonende gezinnen, of deze doelgroep geïnteresseerd is in een bewustere manier verbruiken in het huishouden en welke exacte problemen deze doelgroepen nu hebben bij het analyseren van hun energieverbruik.

# Motivatie onderzoeksmethode

Om meer info te vergaren over deze vragen, heb ik ervoor gekozen om gebruik te maken van de literatuurstudie. De literatuurstudie geeft naar mijn mening een goed eerst beeld over de doelgroep en de goal van het onderzoek. Het is een snelle manier van informatieverzameling en geeft ruimte voor fouten. Wordt er tijdens de studie ondervonden dat de goal en de onderzoeksvragen van het onderzoek naast de kwestie van het brede beeld vallen. Dan is het nog steeds simpel om terug te gaan om de goal en scope wat breder te stellen of op andere aspecten binnen het onderwerp te richten.

# Protocol

Link:

# Resultaten

Aangezien er gericht gezocht is per onderzoeksvraag. Zullen de resultaten ook in die structuur weergegeven worden.
1) Onduidelijkheid rond energieverbruik.

Onderzoeksvraag: Hoe groot is de onduidelijkheid over waar elektriciteit in het huishouden naar toe gaat bij jonge gezinnen?
Expliciet rond de onduidelijkheid van energieverbruik in het huishouden zijn er geen artikelen gevonden. Ook met de bijgeleverde artikelen over andere onderwerpen rond energieverbruik, zoals klimaatstress bij jongeren ben ik niet veel wijzer geworden. Dit resultaat is natuurlijk niet zo raar aangezien de onderzoeksvraag heel erg nauw zocht.

## 2) Energieverbruik in gezinnen

Onderzoeksvraag: Wanneer wordt in een standaard huishouden het meeste energie verbruikt en waar gaat deze dan naar toe?
