Grotesmurf696/ZUIN/img/Droomeiland.pdf

# Mijn droomeiland

Naam: ___________________________
Leerjaar: ______________________________

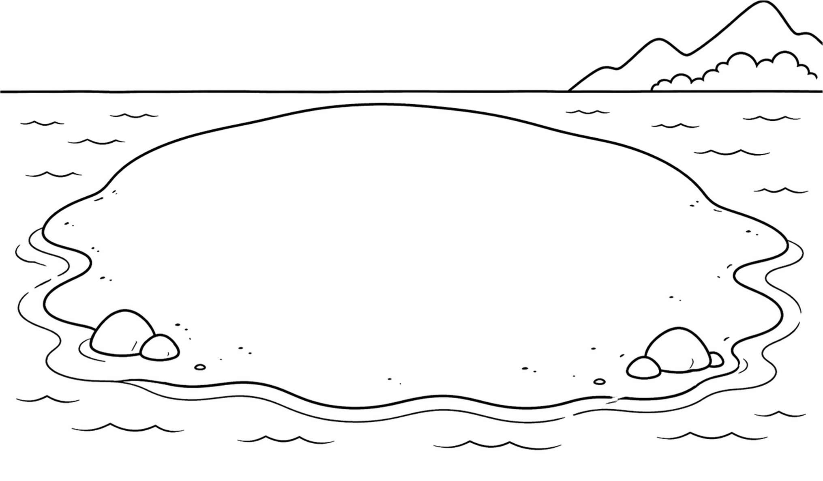
[picture p84: figure]
