Grotesmurf696/ZUIN/cad/Develop 2/Import/grove-16x2-lcd-black-on-yellow-1.snapshot.3/Grove-16x2 LCD Front (Black and Yellow).png

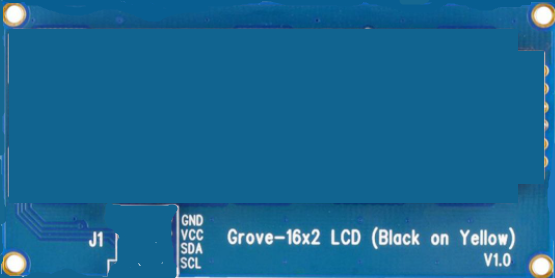
cad/Develop 2/Import/grove-16x2-lcd-black-on-yellow-1.snapshot.3/Grove-16x2 LCD Front (Black and Yellow).png
