Grotesmurf696/ZUIN/img/Double Diamond.jpg

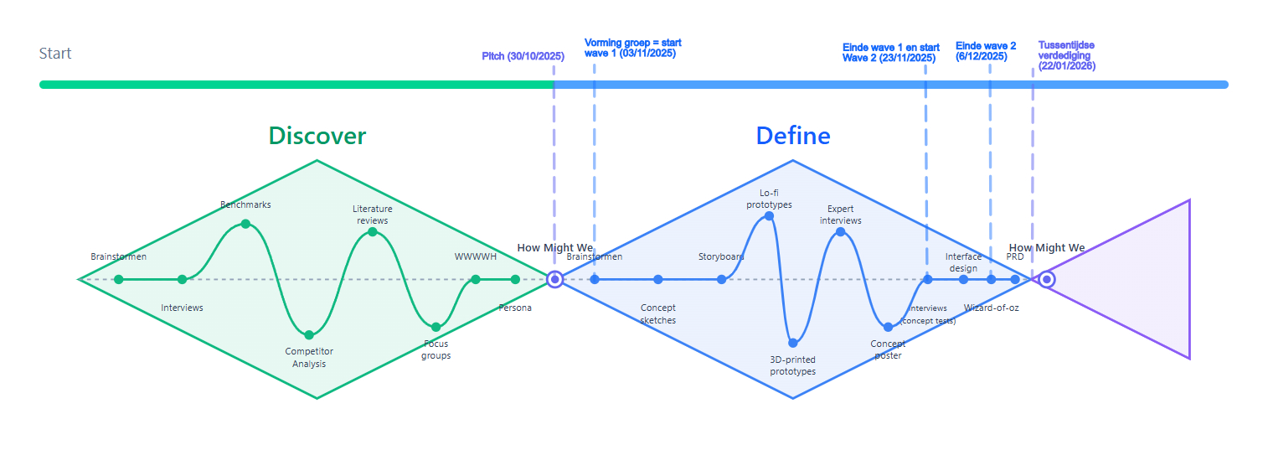
img/Double Diamond.jpg
