Grotesmurf696/ZUIN/img/Double Diamond.png

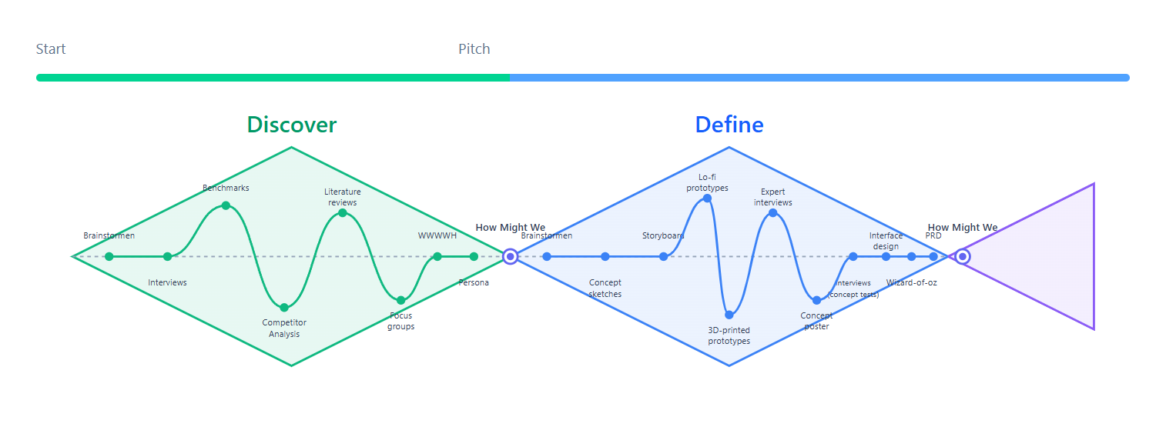
img/Double Diamond.png
