Grotesmurf696/ZUIN/img/Eerste_Prototypes.JPG

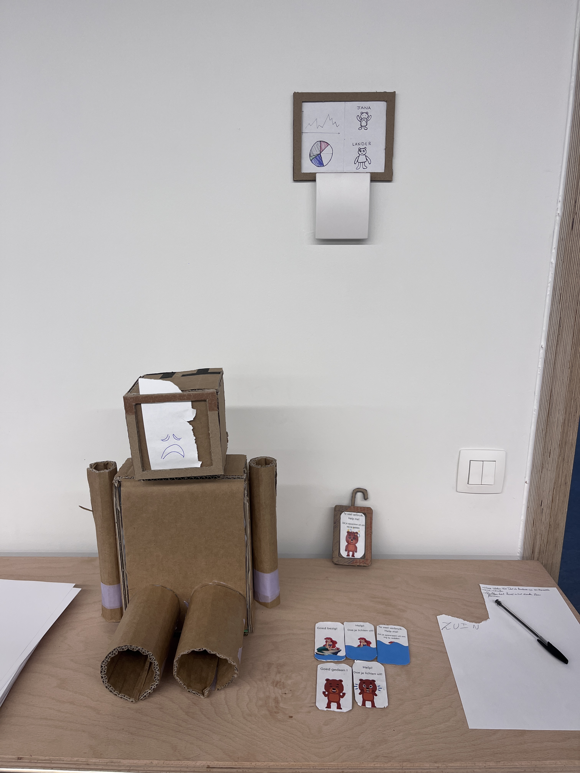
img/Eerste_Prototypes.JPG
