Grotesmurf696/ZUIN/img/Lateral_pinch_strength.jpg

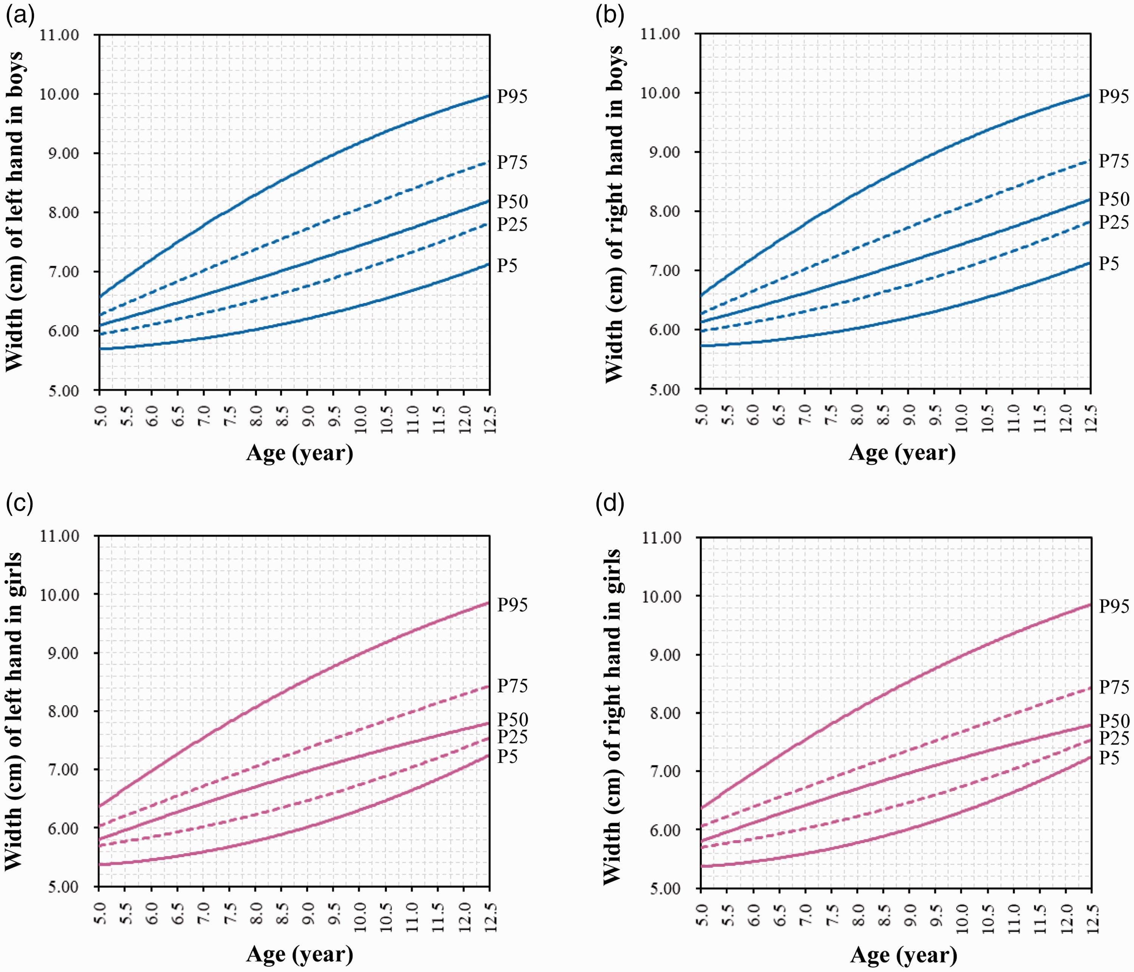
img/Lateral_pinch_strength.jpg
