Grotesmurf696/ZUIN/img/Leaf_Mascotte.png

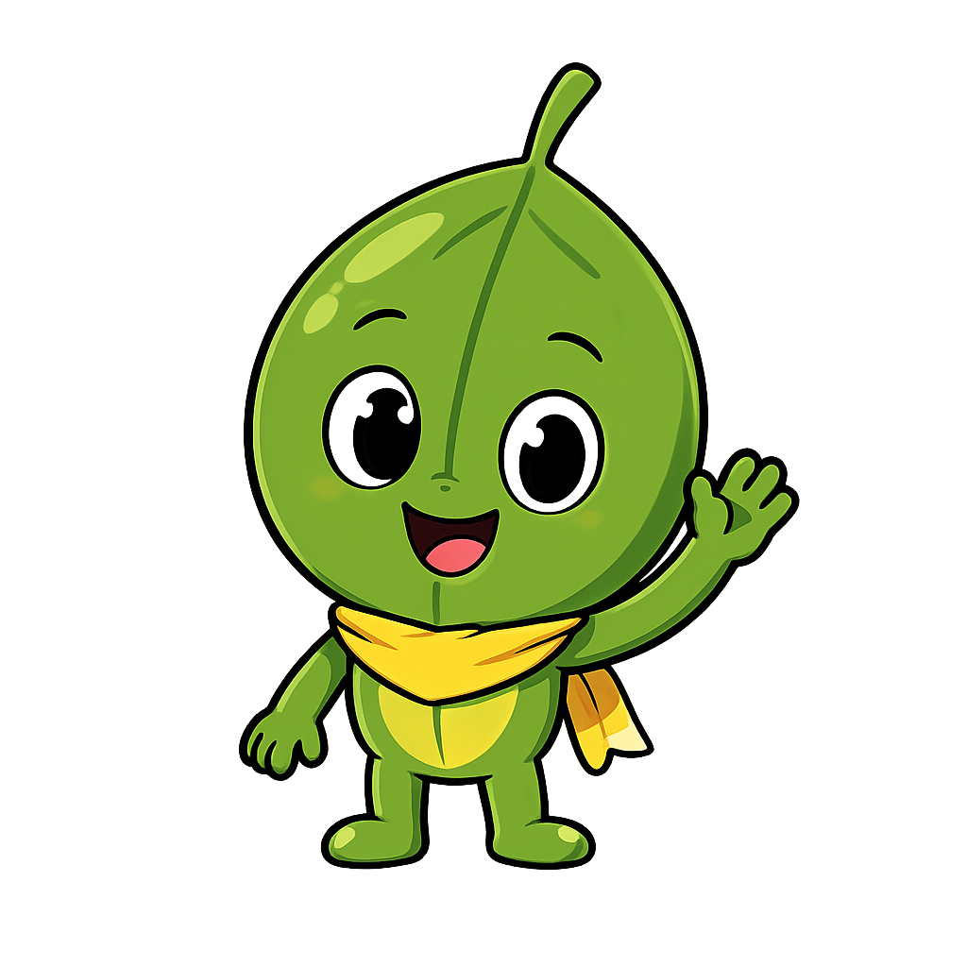
img/Leaf_Mascotte.png
