Grotesmurf696/ZUIN/img/MVP2.png

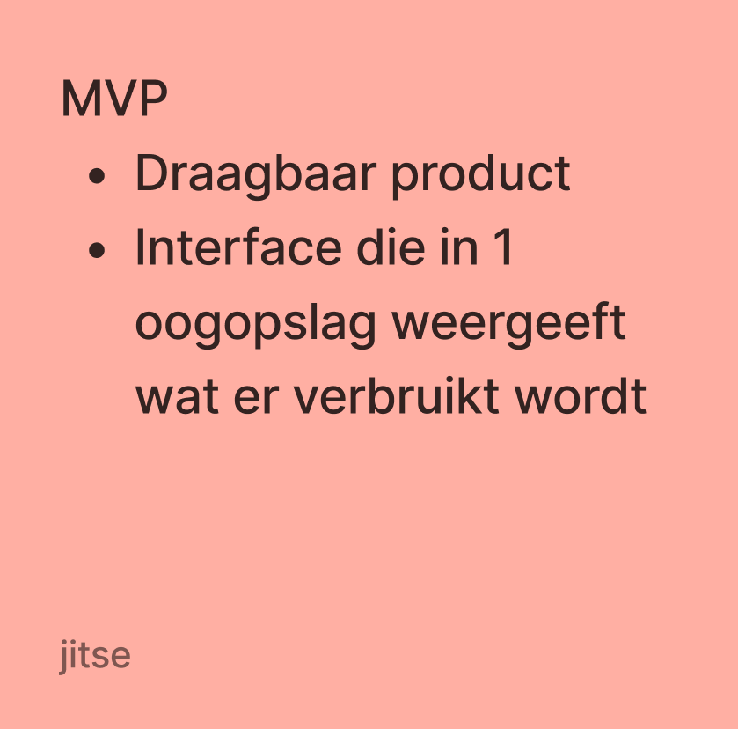
img/MVP2.png
