Grotesmurf696/ZUIN/img/Render Zuin horloge V1.png

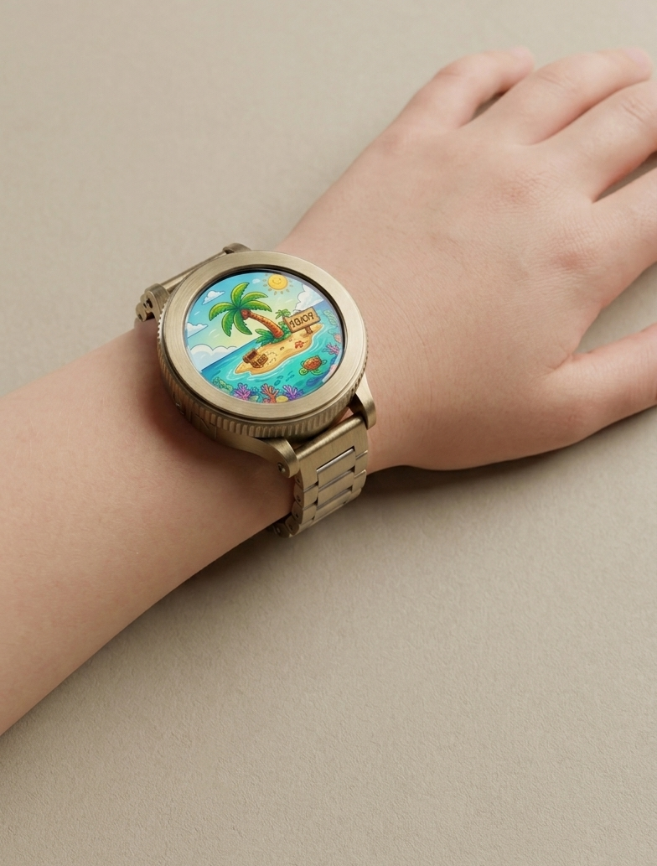
img/Render Zuin horloge V1.png
