Grotesmurf696/ZUIN/img/Render ZUÏN.jpeg

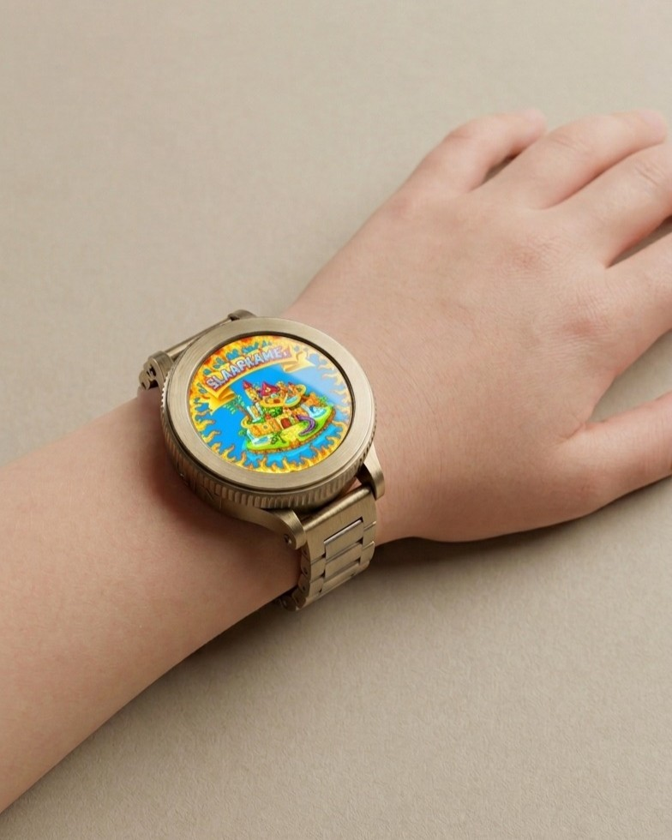
img/Render ZUÏN.jpeg
