Grotesmurf696/ZUIN/img/Tripple_Diamond2.jpg

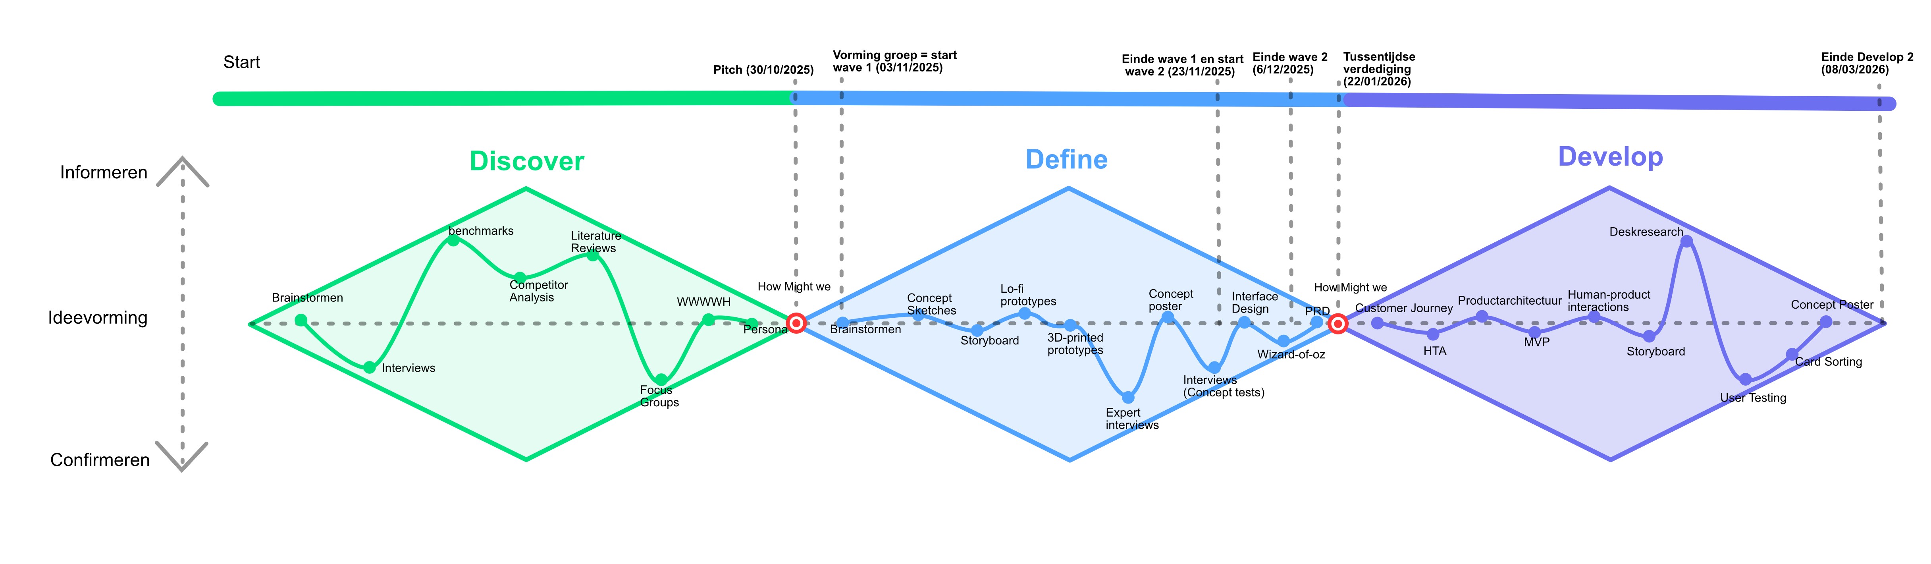
img/Tripple_Diamond2.jpg
