Grotesmurf696/ZUIN/cad/Develop 3/base horloge.3mf

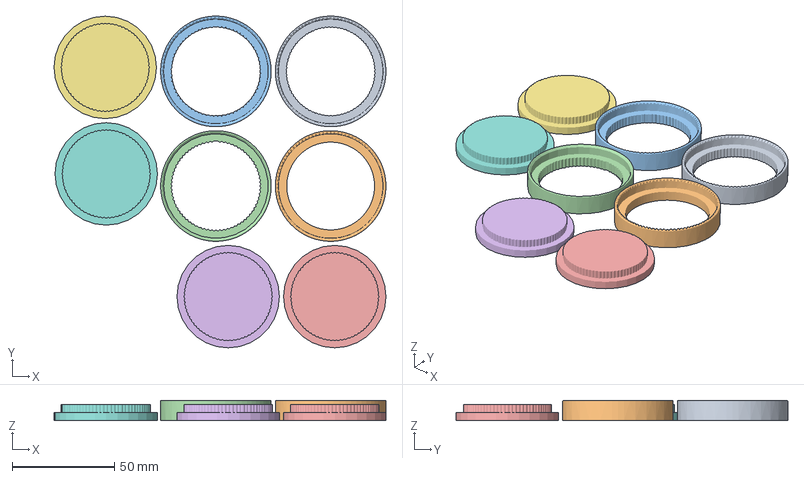
[picture p117: CAD file, 2026-05-22]
cad/Develop 3/base horloge.3mf
162.0 x 161.8 x 10.0 mm
Ring 1.stl
Ring 2.stl
Ring 3.stl
Ring 4.stl
base horloge.stl x 4
