Grotesmurf696/ZUIN/cad/Develop 2/Import/grove-16x2-lcd-black-on-yellow-1.snapshot.3/PCB.SLDPRT

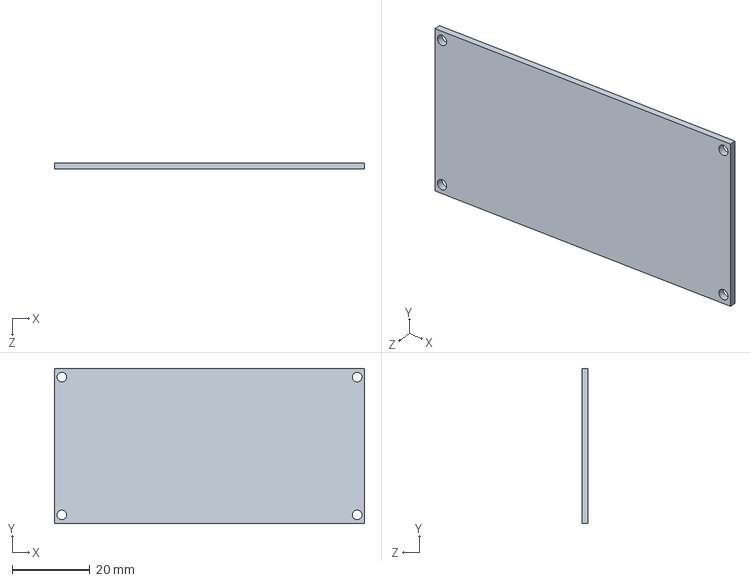
[picture p118: CAD file, 2026-05-22]
cad/Develop 2/Import/grove-16x2-lcd-black-on-yellow-1.snapshot.3/PCB.SLDPRT
80.0 x 40.0 x 1.60 mm
