Grotesmurf696/ZUIN/cad/Develop 2/Import/grove-imu-9-dof-v1-1.snapshot.1/MPU9150.SLDPRT

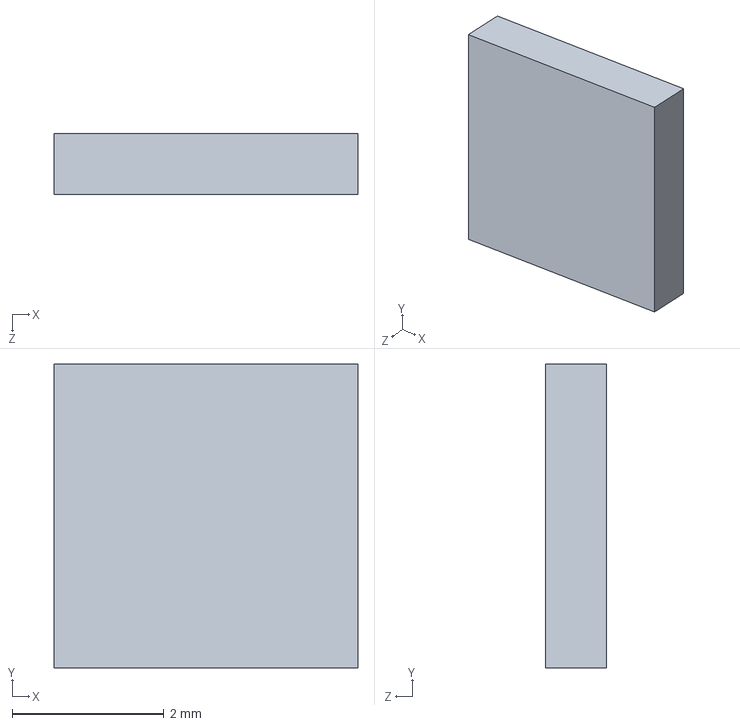
[picture p119: CAD file, 2026-05-22]
cad/Develop 2/Import/grove-imu-9-dof-v1-1.snapshot.1/MPU9150.SLDPRT
4.00 x 4.00 x 0.8 mm
