Grotesmurf696/ZUIN/cad/Develop 2/Import/grove-16x2-lcd-black-on-yellow-1.snapshot.3/Bloc alim.SLDPRT

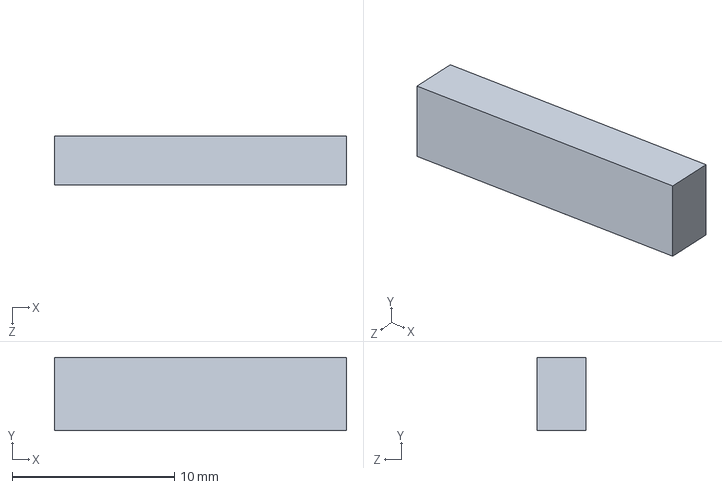
[picture p121: CAD file, 2026-05-22]
cad/Develop 2/Import/grove-16x2-lcd-black-on-yellow-1.snapshot.3/Bloc alim.SLDPRT
18.0 x 4.50 x 3.00 mm
