Grotesmurf696/ZUIN/cad/Develop 2/SV-Wearable_Bovenkant-001.stp

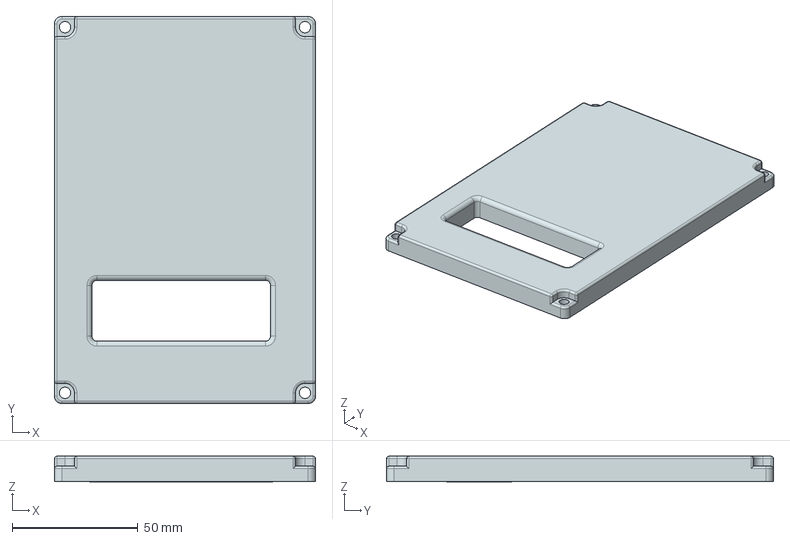
[picture p122: CAD file, 2026-05-22]
cad/Develop 2/SV-Wearable_Bovenkant-001.stp
104.0 x 154.0 x 10.2 mm
