Grotesmurf696/ZUIN/reports and protocols/Define/Wave 2/Gesprek Comon.pdf

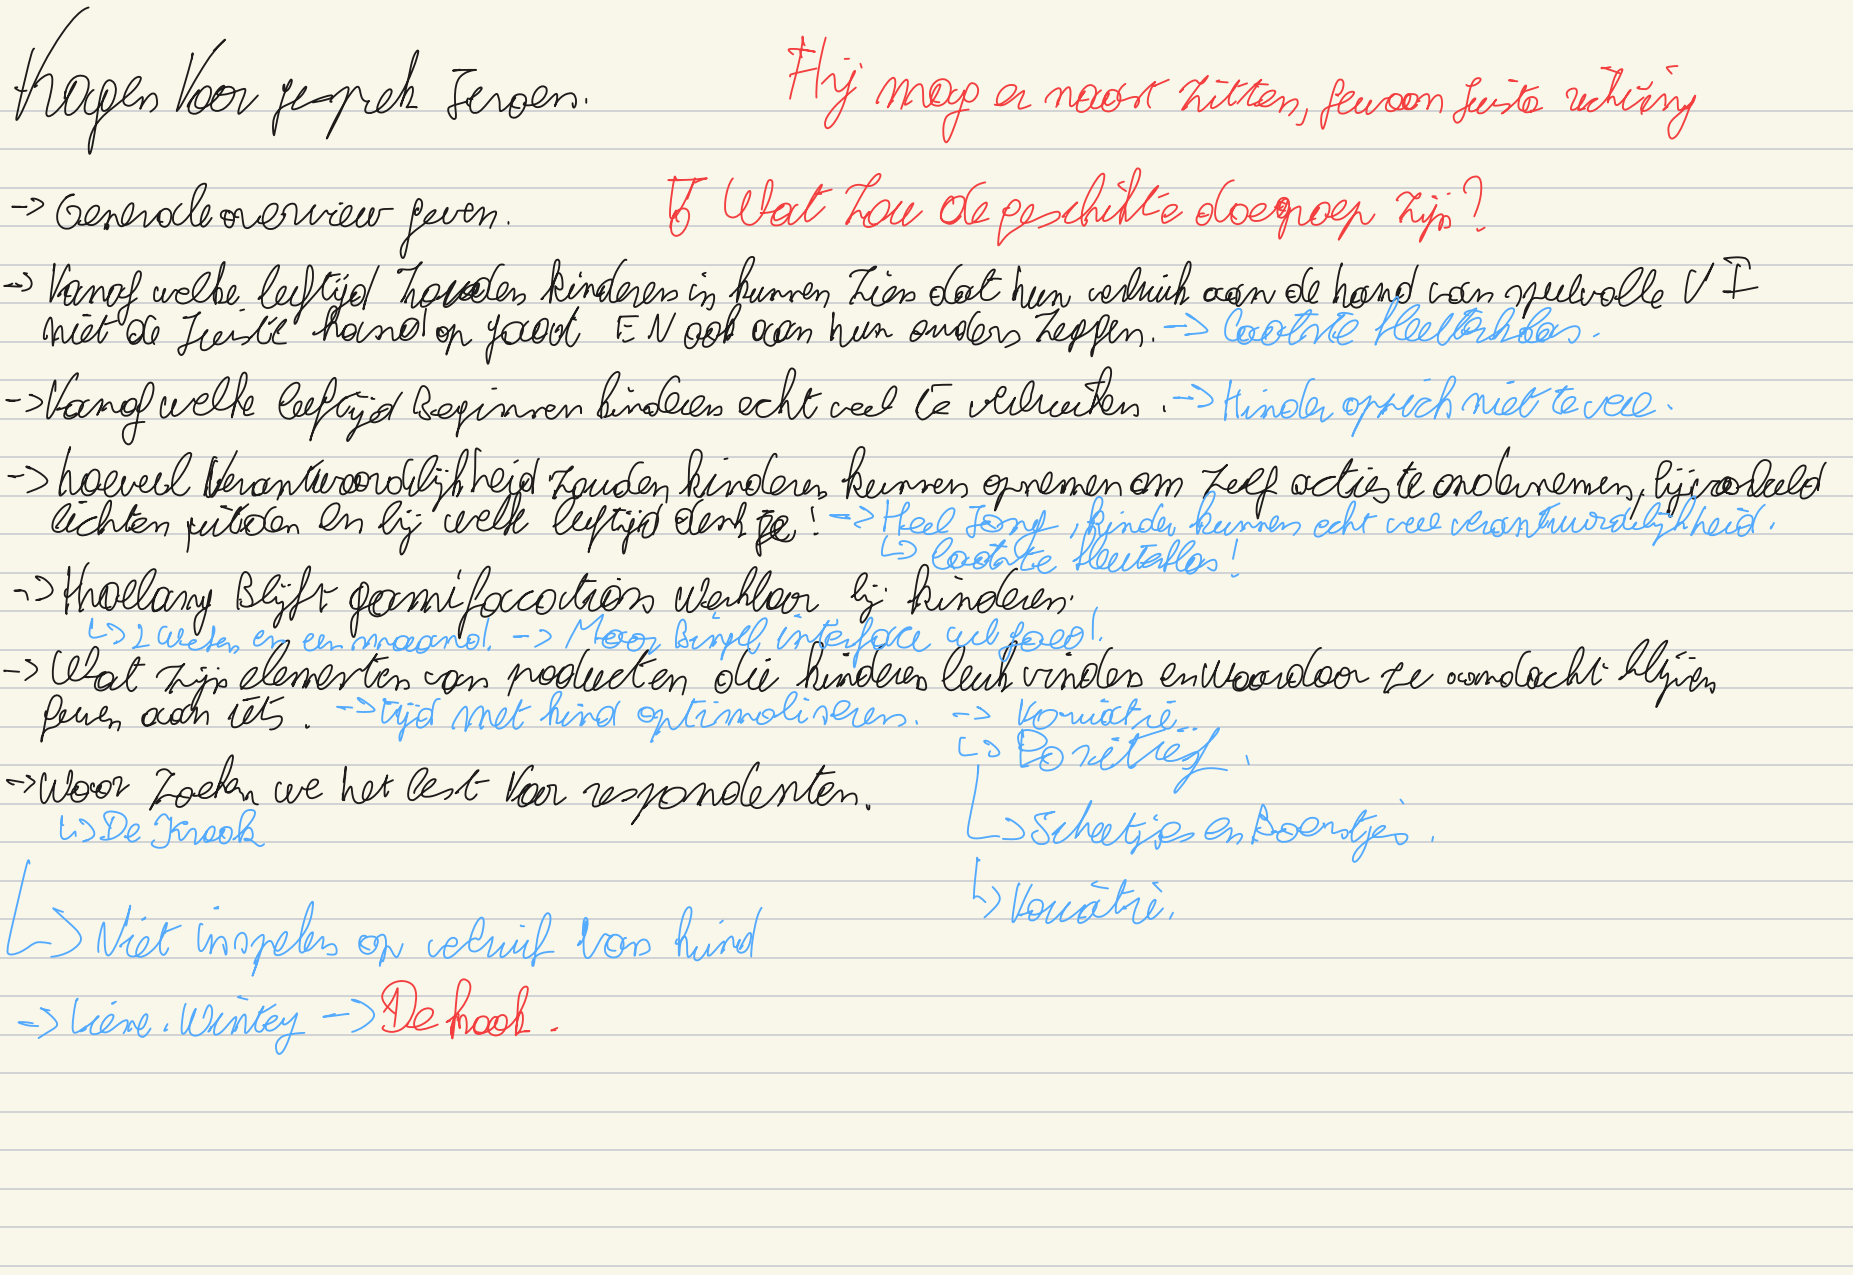
[picture p129: page 1]
