Grotesmurf696/ZUIN/img/Tamagotchi_V2.JPG

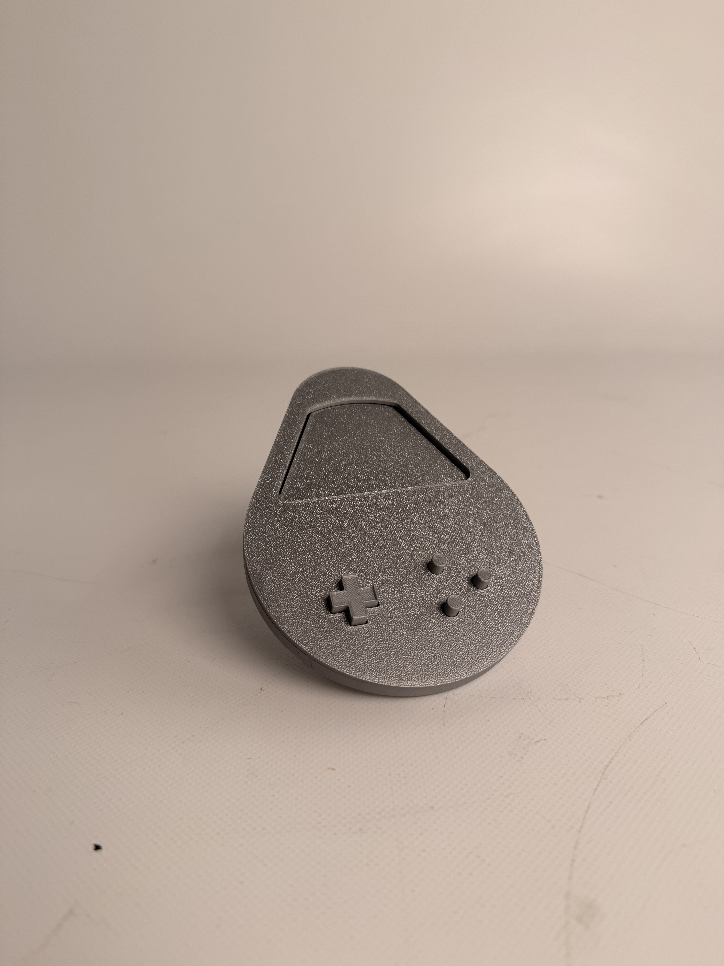
img/Tamagotchi_V2.JPG
